woytekm/IRIS2/Code/IRIS2/audio/AMP-TAS5721.h

// pin mappings are for "WM Project AMP 0.1 v3 2.1" HAT Board 

#define AMP_TAS5721_HEADPHONE_AMP RPI_BPLUS_GPIO_J8_37
#define AMP_TAS5721_FAULT_I2C     RPI_BPLUS_GPIO_J8_32
#define AMP_TAS5721_RESET         RPI_BPLUS_GPIO_J8_36
#define AMP_TAS5721_PWR           RPI_BPLUS_GPIO_J8_38

#define TAS5721_I2C_ADDR 0x1b
#define TAS5721_I2C_ID   0x6c
#define TAS5721_I2C_BAUDRATE 10000

/* only registers useful for basic operation */

#define TAS5721_I2C_REG_CLKCTRL   0x00
#define TAS5721_I2C_REG_ERRSTAT   0x02
#define TAS5721_I2C_REG_SERDAT    0x04
#define TAS5721_I2C_REG_OSCTRIM   0x1b
#define TAS5721_I2C_REG_CH4SRC    0x21
#define TAS5721_I2C_REG_SOFTMUTE  0x06
#define TAS5721_I2C_REG_SYSCTRL2  0x05
#define TAS5721_I2C_REG_MASTERVOL 0x07
#define TAS5721_I2C_REG_CH1VOL    0x08
#define TAS5721_I2C_REG_CH2VOL    0x09

#define AMP_TAS5721_INIT_SATELLITE_GAIN   0x15
#define AMP_TAS5721_INIT_SUBWOOFER_GAIN   0x04 
#define AMP_TAS5721_INIT_MASTERVOL        0x35

uint8_t G_TAS5721_detected;
